ArcAttack/FieldMill-PCB/Pictures/Image-5.jpg

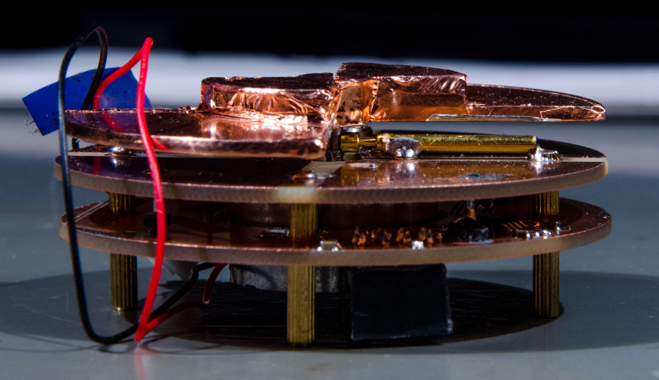
Pictures/Image-5.jpg
