ArcAttack/FieldMill-PCB/Pictures/Image-6.jpg

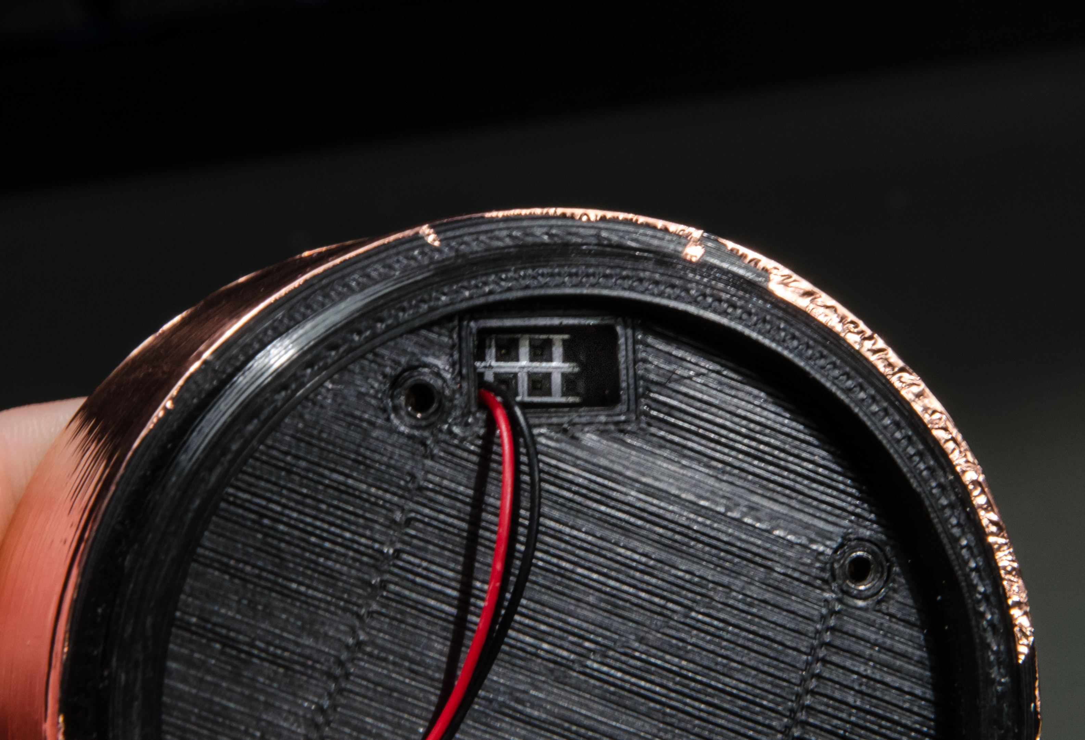
Pictures/Image-6.jpg
